OLIMEX/ESP32-EVB/HARDWARE/REV-K2/3d/User Library-GP1UE26.STEP

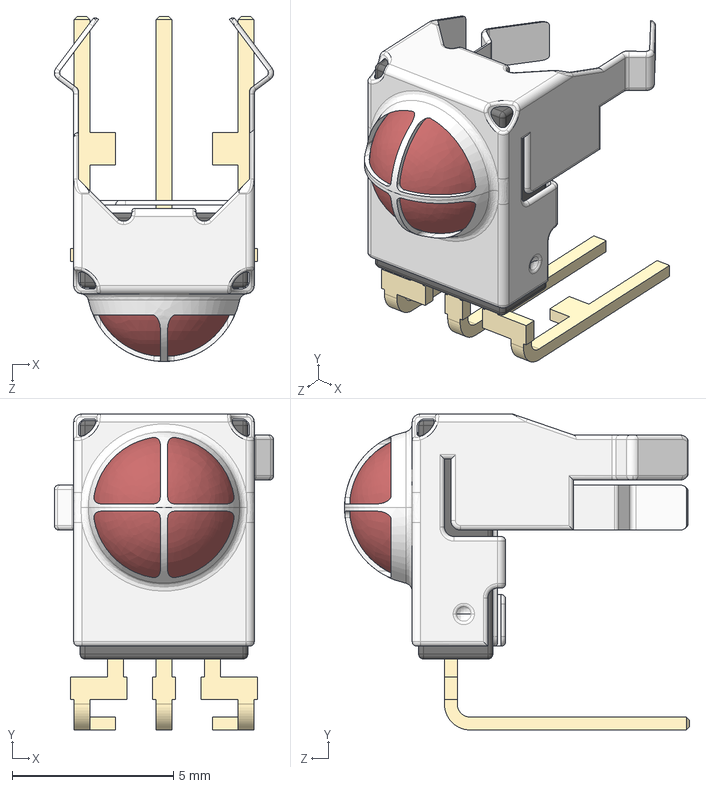
[picture p20: CAD file, 2020-01-02]
HARDWARE/REV-K2/3d/User Library-GP1UE26.STEP
6.80 x 9.80 x 10.7 mm
