OLIMEX/ESP32-EVB/HARDWARE/REV-K2/3d/BAT54.step

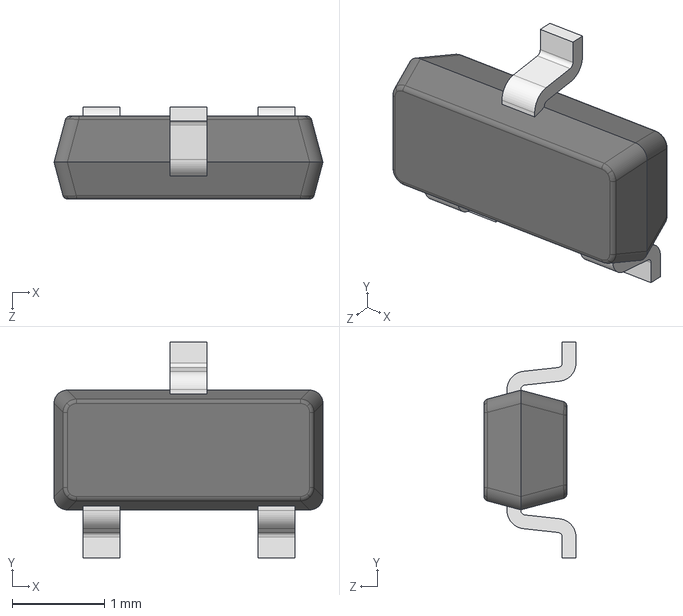
[picture p21: CAD file, 2020-01-02]
HARDWARE/REV-K2/3d/BAT54.step
2.92 x 2.34 x 1.00 mm
