OLIMEX/ESP32-EVB/HARDWARE/REV-K2/3d/TEConnectivity -ORWH-SH-124D1F000.stp

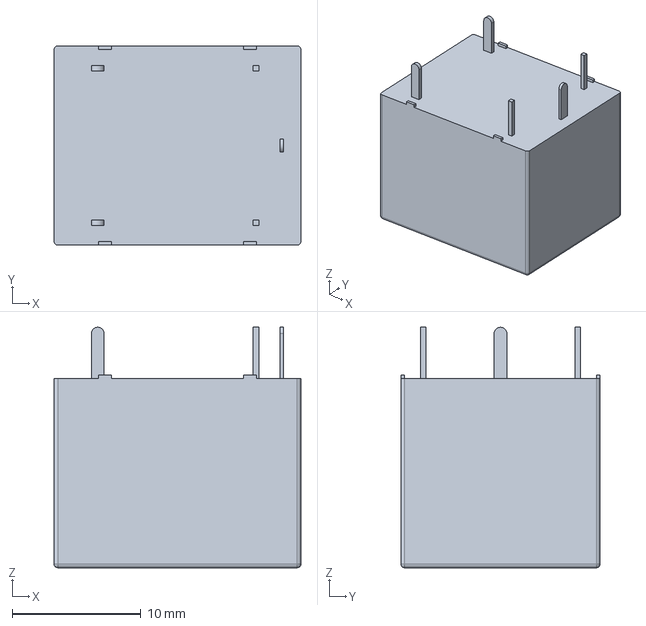
[picture p22: CAD file, 2020-01-02]
HARDWARE/REV-K2/3d/TEConnectivity -ORWH-SH-124D1F000.stp
19.2 x 15.5 x 18.7 mm
