OLIMEX/ESP32-EVB/HARDWARE/REV-K2/3d/SOT-23-5.step

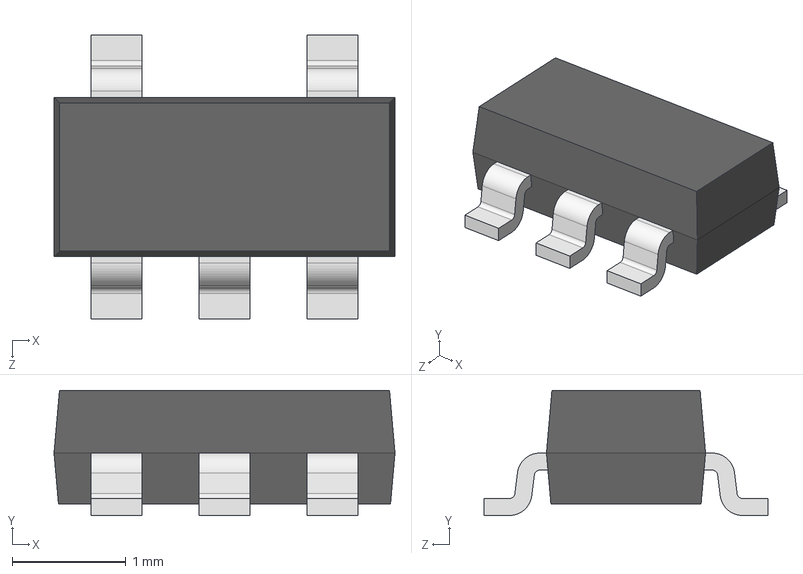
[picture p23: CAD file, 2020-01-02]
HARDWARE/REV-K2/3d/SOT-23-5.step
3.00 x 1.10 x 2.50 mm
