OLIMEX/ESP32-EVB/HARDWARE/REV-K2/3d/SO-8_150mil---SN65HVDA1050AQDRQ1.STEP

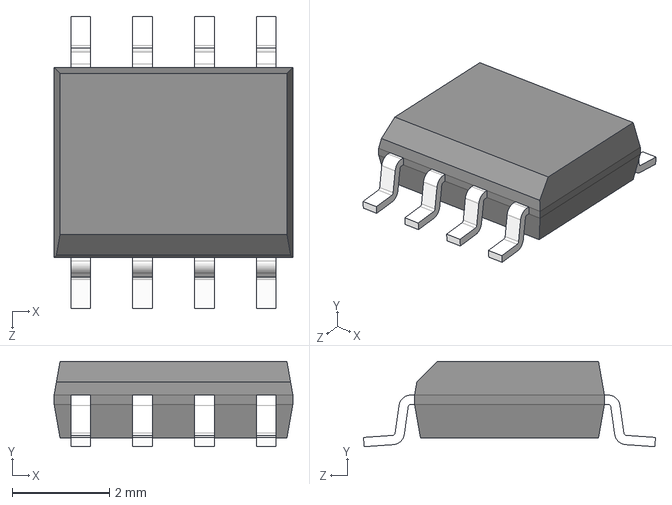
[picture p24: CAD file, 2020-01-02]
HARDWARE/REV-K2/3d/SO-8_150mil---SN65HVDA1050AQDRQ1.STEP
4.90 x 1.75 x 5.99 mm
