OLIMEX/ESP32-EVB/HARDWARE/REV-K2/3d/JST_B2B-PH-SM4-TB(DW02R).step

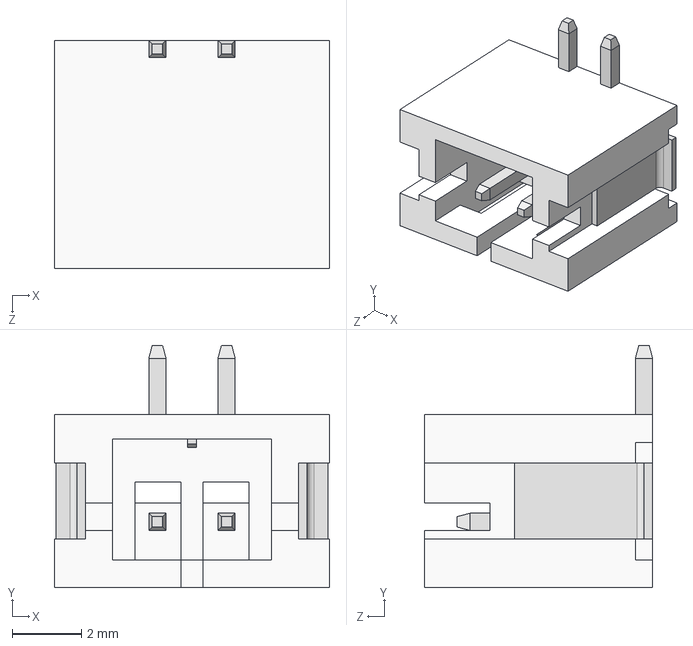
[picture p25: CAD file, 2020-01-02]
HARDWARE/REV-K2/3d/JST_B2B-PH-SM4-TB(DW02R).step
7.95 x 7.00 x 6.60 mm
