OLIMEX/ESP32-EVB/HARDWARE/REV-K2/3d/User_Library-Crystal_HC49_US-SM.step

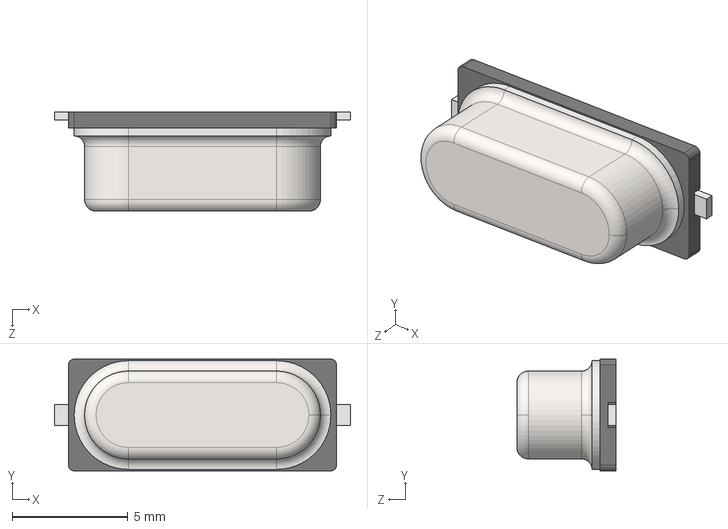
[picture p27: CAD file, 2020-01-02]
HARDWARE/REV-K2/3d/User_Library-Crystal_HC49_US-SM.step
12.8 x 4.83 x 4.30 mm
