OLIMEX/ESP32-EVB/HARDWARE/REV-K2/3d/BH-10__64.step

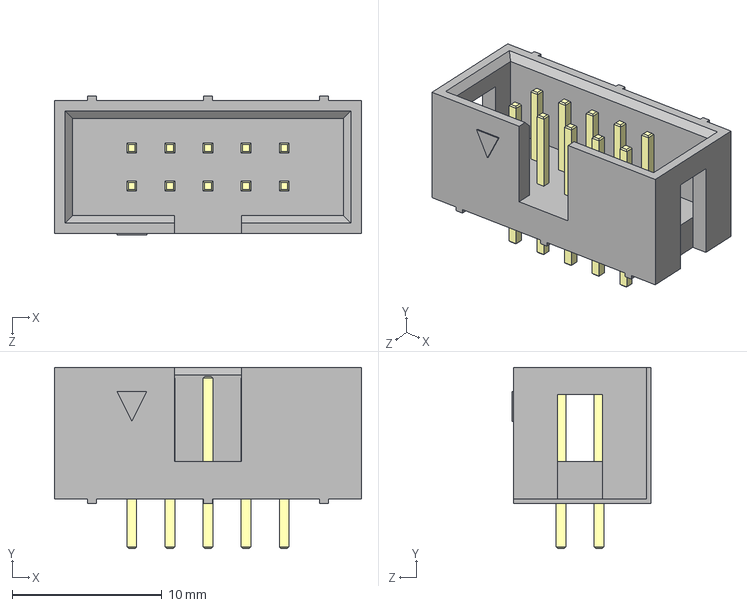
[picture p28: CAD file, 2020-01-02]
HARDWARE/REV-K2/3d/BH-10__64.step
20.5 x 12.1 x 9.30 mm
