OLIMEX/ESP32-EVB/HARDWARE/REV-K2/3d/SOD123.step

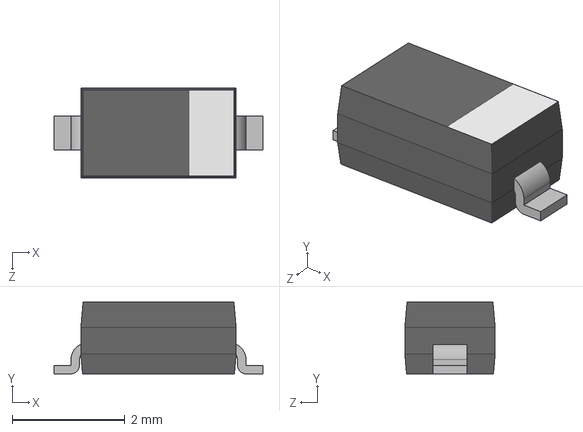
[picture p29: CAD file, 2020-01-02]
HARDWARE/REV-K2/3d/SOD123.step
3.70 x 1.27 x 1.60 mm
