OLIMEX/ESP32-EVB/HARDWARE/REV-K2/3d/pj-102ah.stp

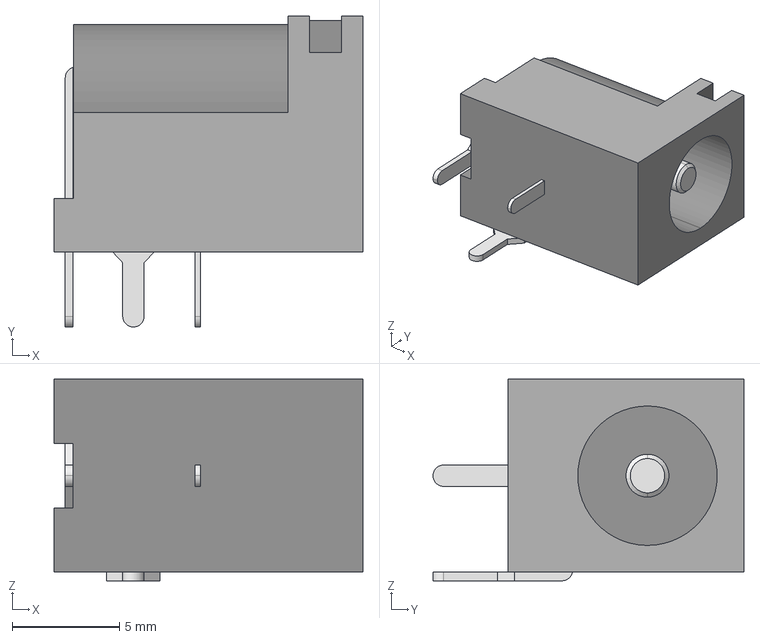
[picture p30: CAD file, 2020-01-02]
HARDWARE/REV-K2/3d/pj-102ah.stp
14.4 x 14.5 x 9.40 mm
