OLIMEX/ESP32-EVB/HARDWARE/REV-K2/3d/esp-wroom-32.step

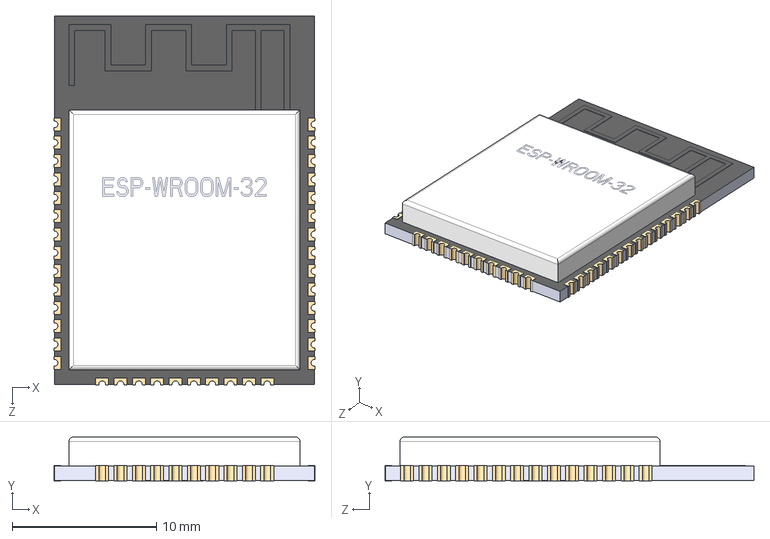
[picture p31: CAD file, 2020-01-02]
HARDWARE/REV-K2/3d/esp-wroom-32.step
18.1 x 3.04 x 25.5 mm
