OLIMEX/ESP32-EVB/HARDWARE/REV-H/ESP32-EVB_Rev_H-BOM.pdf

ESP32-EVB_Rev_H-BOM | 04/24/2019

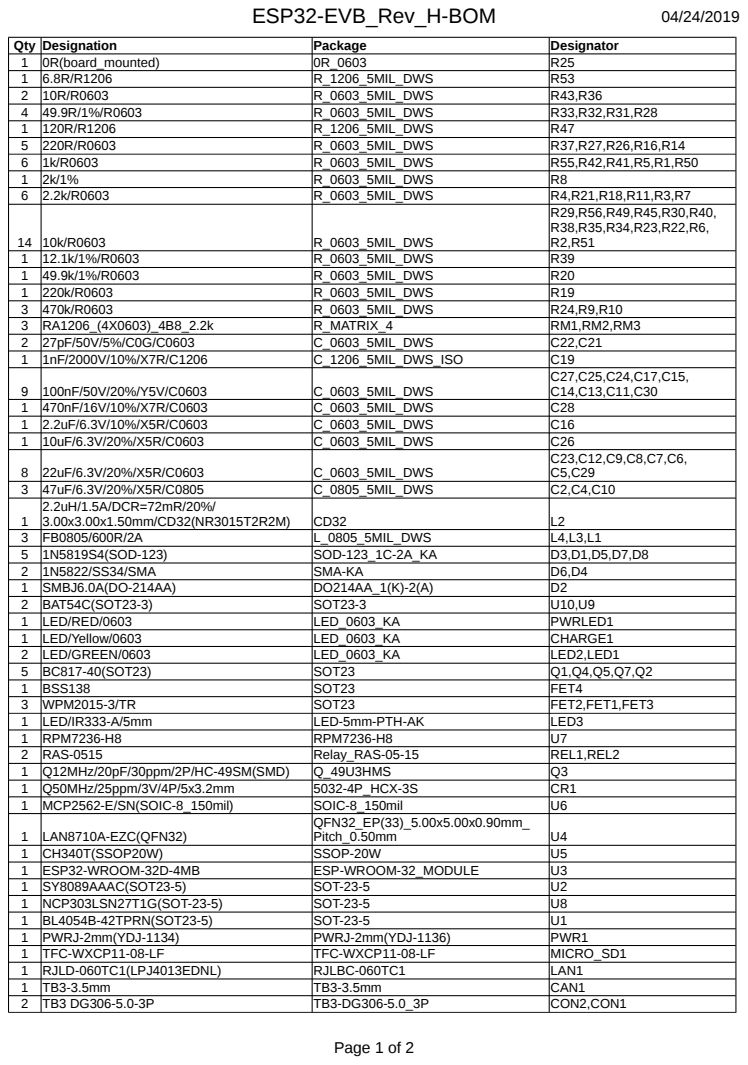
[picture p37: page 1]

| ESP32-EVB_Rev_H-BOM | 04/24/2019
1 BH10S | UEXT_ML10 | UEXT1
1 MISB-SWMM-5B-LF(USB_MICRO) | USB-MICRO_MISB-SWMM-5B_LF | USB-UART1
1 DW02R | LIPO_BAT-CON2DW02R | BAT1
2 T1107A(6x3,8x2,5MM) | T1107A(6x3,8x2,5MM) | RST1,BUT1
2 Opened | SJ | CAN_T1,PHY_RST1
1 Closed(1-2)/Opened(2-3) | SJ_2_SMALL_12_TIED | 5.0V/3.3V1
1 Opened(2-3)/Soldered(1-2) | SJ_2_SMALL | BAT/BUT1
1 NA(1k/R0603) | R_0603_5MIL_DWS | R57
5 NA/R0603 | R_0603_5MIL_DWS | R44,R54,R48,R46,R17
2 NA(47uF/6.3V/20%/X5R/C0805) | C_0805_5MIL_DWS | C3,C1
1 NA(1nF/2000V/10%/X7R/C1206) | C_1206_5MIL_DWS_ISO | C20
1 NA(HN2x20) | HN2x20 | EXT1
1 NA(TB2 DG306-5.0-2P) | TB2-DG306-5.0_2P | PWR2
1 NA(10uF/6.3V/20%/X5R/C0603) | C_0603_5MIL_DWS | C18
1 NA(FB0805/600R/2A) | L_0805_5MIL_DWS | L5
