OLIMEX/ESP32-EVB/HARDWARE/REV-H/ESP32-EVB_Rev_H.pdf

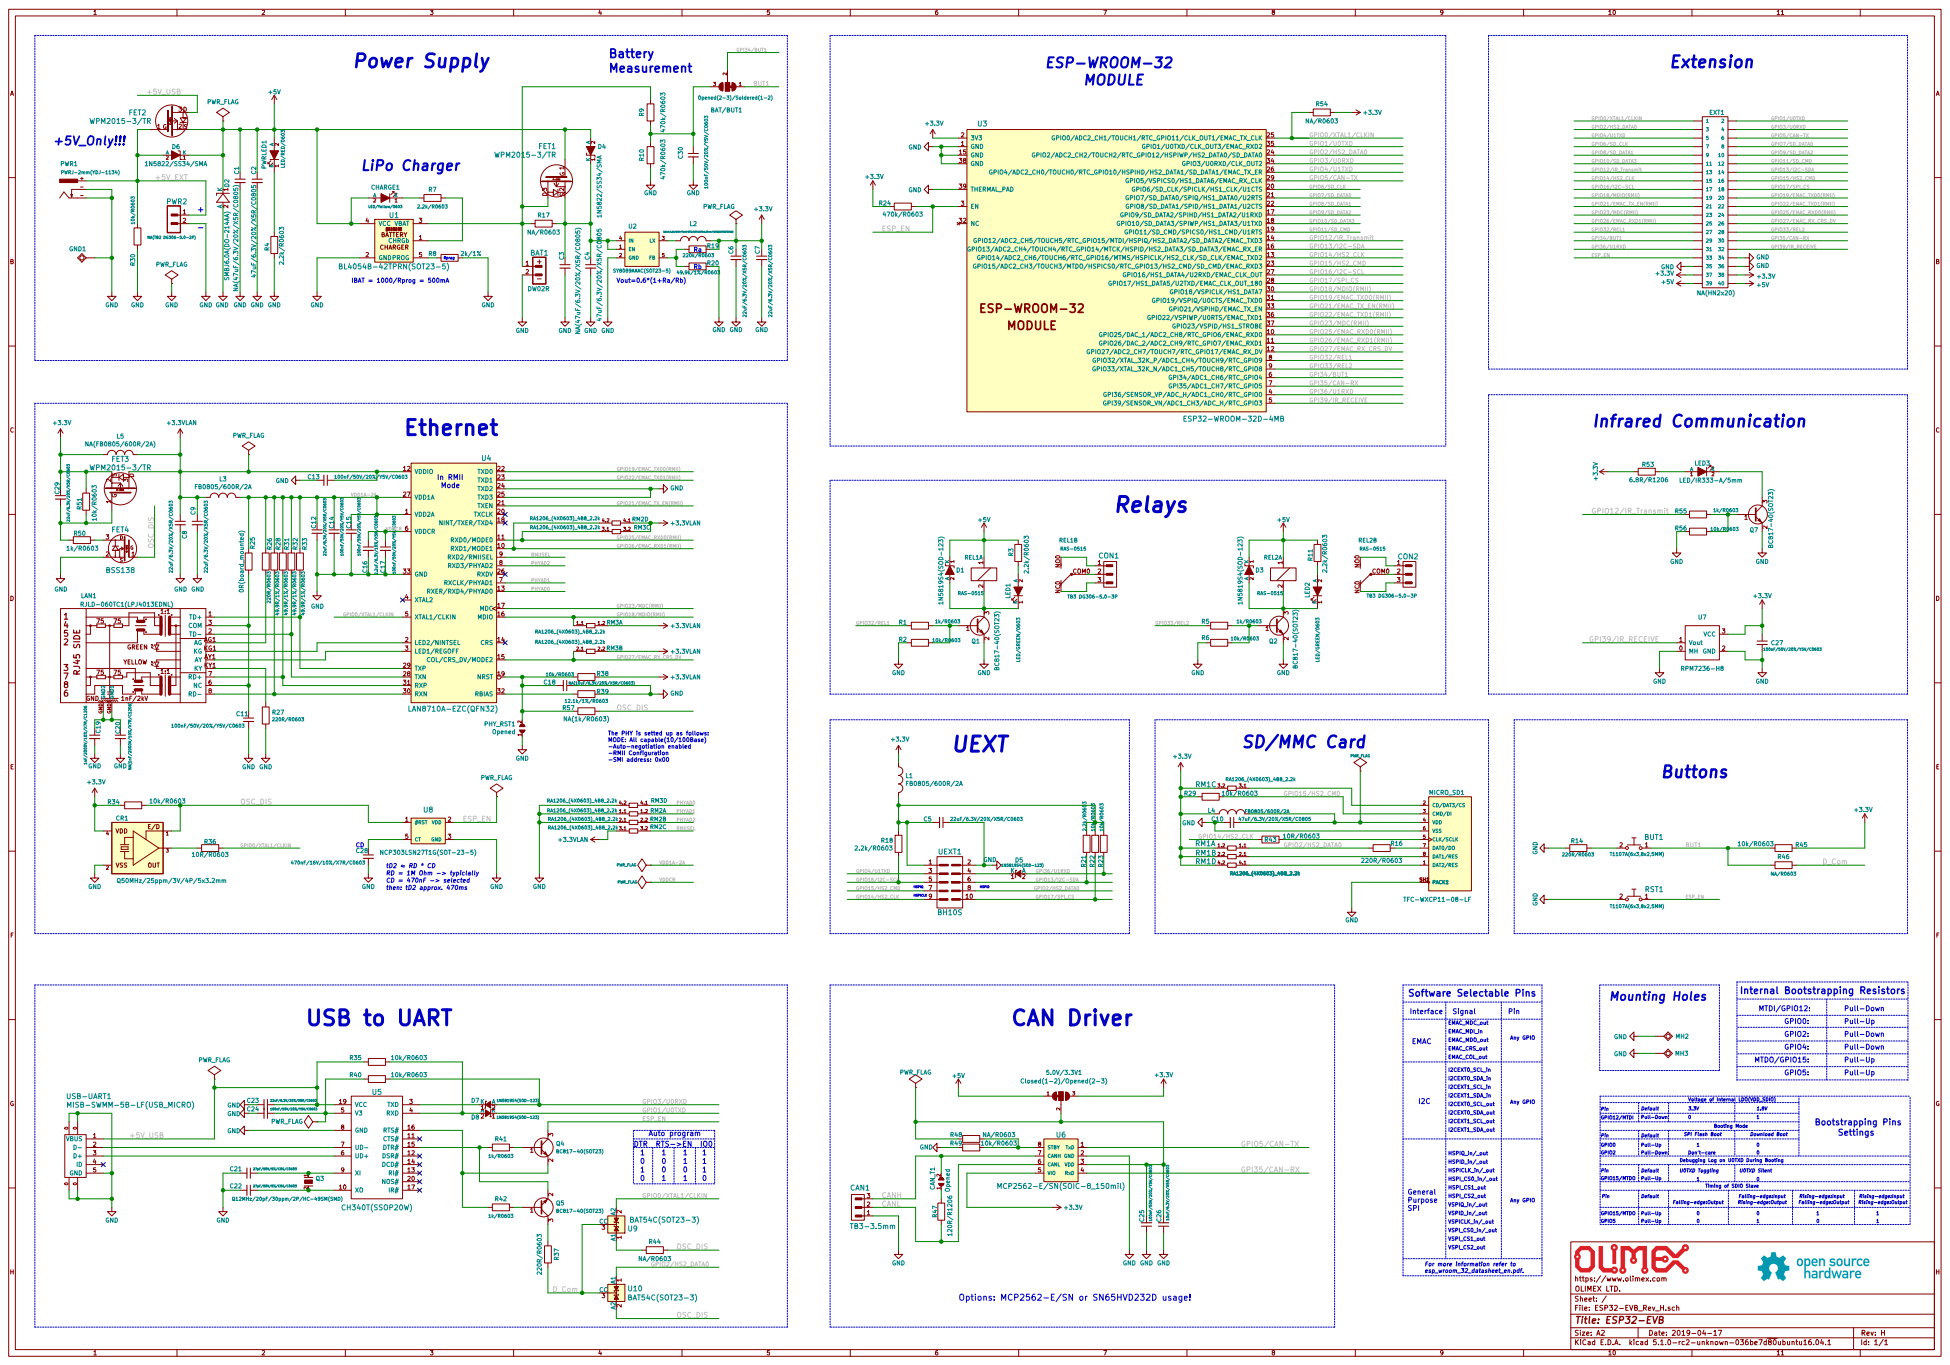
[picture p38: page 1]

2 PWRLED1 LED/RED/0603 GND GND GND GND GND

VDDCR The PHY is setted up as follows: MODE: All capable(10/100Base)

RD = 1M Ohm -> typiclally CD = 470nF -> selected

MISB-SWMM-5B-LF(USB_MICRO) GND

File: ESP32-EVB_Rev_H.sch Sheet: / OLIMEX LTD. https://www.olimex.com

Options: MCP2562-E/SN or SN65HVD232D usage!
