OLIMEX/ESP32-EVB/HARDWARE/REV-F/ESP32-EVB_Rev_F.pdf

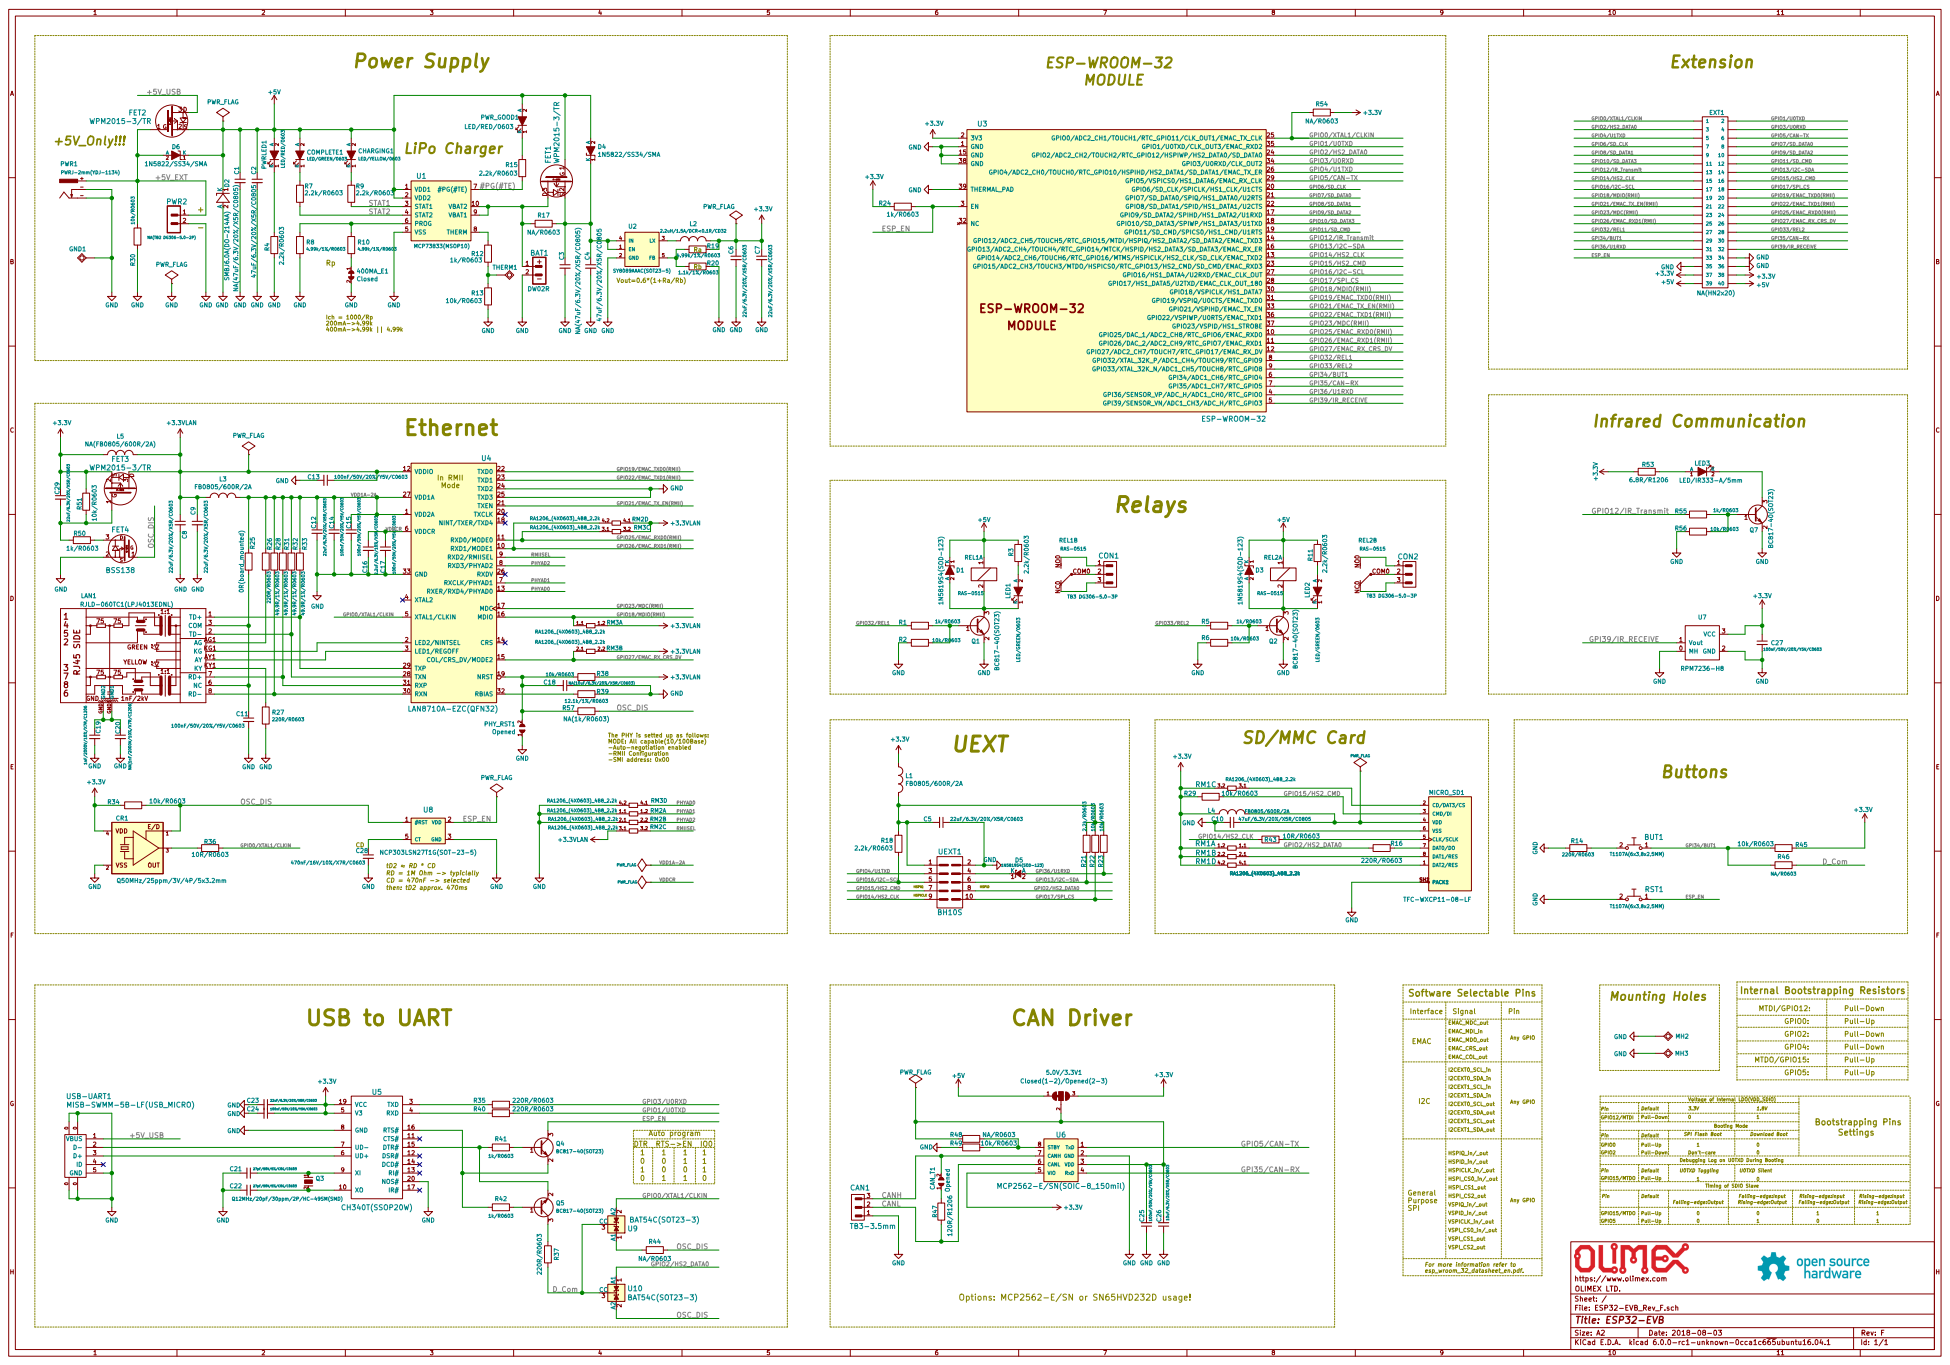
[picture p40: page 1]

2 PWRLED1 LED/RED/0603 GND GND GND GND GND

2.2uH/1.5A/DCR<0.1R/CD32 R19
GPIO13/I2C-SDA GPIO19/EMAC_TXD0(RMII) GPIO22/EMAC_TXD1(RMII) GPIO21/EMAC_TX_EN(RMII) GND

VDDCR The PHY is setted up as follows: MODE: All capable(10/100Base)
-Auto-negotiation enabled
-RMII Configuration
-SMI address: 0x00

PWR_FLAG
DAT2/RES 1 CD/DAT3/CS 2 CMD/DI 3 VDD 4 CLK/SCLK 5 VSS 6 DAT0/DO 7 DAT1/RES 8 PACK1 SH1 PACK2 SH2MICRO_SD1 TFC-WXCP11-08-LF

RD = 1M Ohm -> typiclally CD = 470nF -> selected

File: ESP32-EVB_Rev_F.sch Sheet: / OLIMEX LTD. https://www.olimex.com
