OLIMEX/ESP32-EVB/HARDWARE/REV-D/ESP32-EVB_Rev_D.pdf

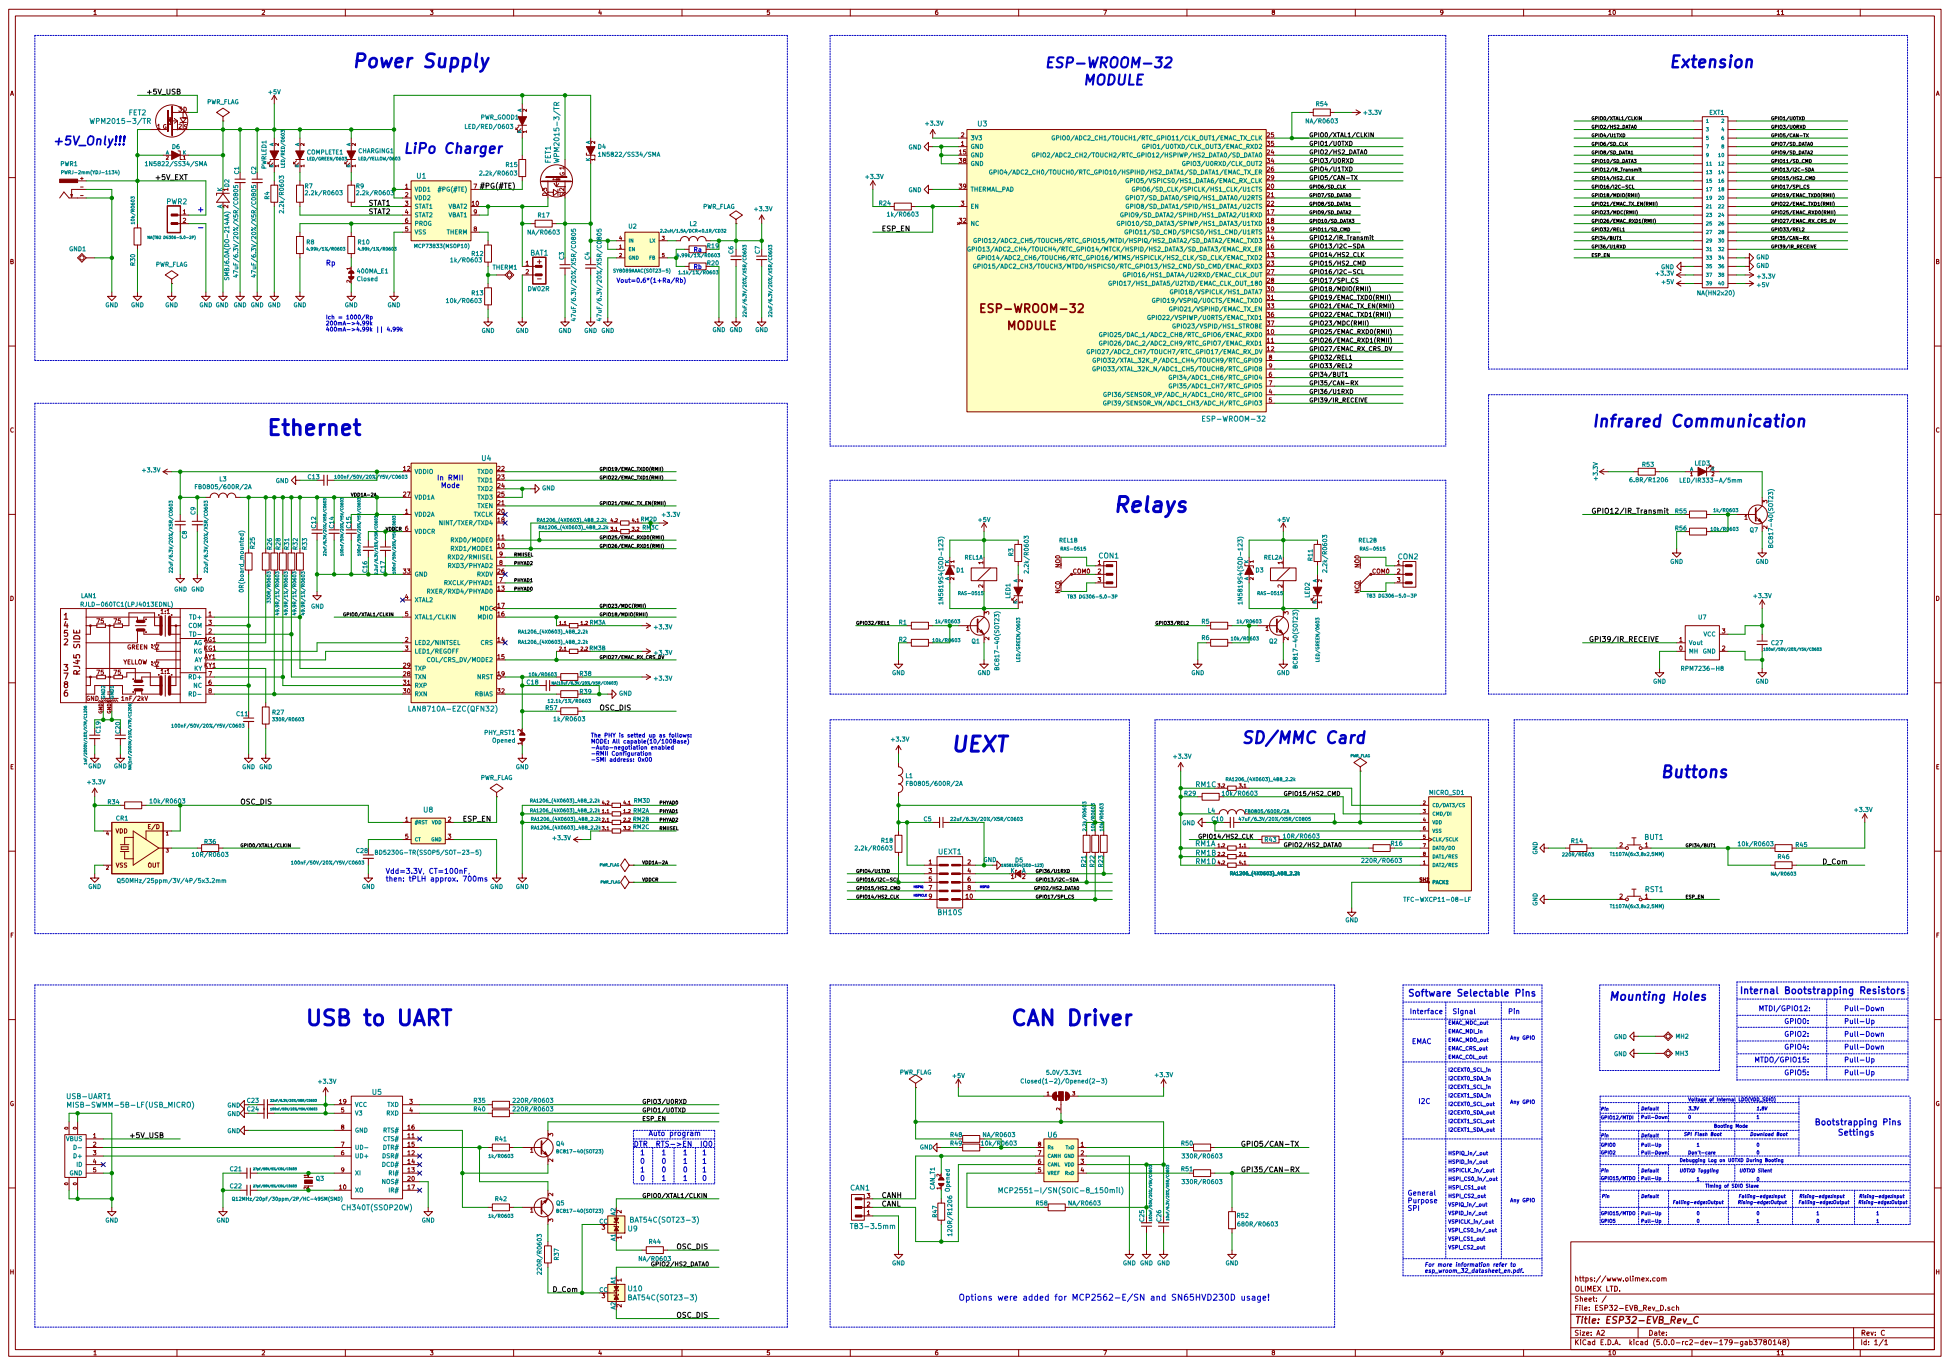
[picture p41: page 1]

2 PWRLED1 LED/RED/0603 GND GND GND GND GND

TD+ 1 TD- 2 COM 3 NC 6 RD+ 7 RD- 8 AG AG1 KG KG1 AY AY1 KY KY1 GND1 GND1 GND2 GND2 LAN1 RJLD-060TC1(LPJ4013EDNL)

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

MISB-SWMM-5B-LF(USB_MICRO) GND

VREF 5 CANL 6 CANH 7 Rs 8 U6 MCP2551-I/SN(SOIC-8_150mil) GND

File: ESP32-EVB_Rev_D.sch Sheet: / OLIMEX LTD. https://www.olimex.com
