OLIMEX/ESP32-EVB/SOFTWARE/ESP-IDF examples/toggle_relay/main/toggle_relay.c

// Copyright (c) 2017 Olimex LTD.
//
// GNU GENERAL PUBLIC LICENSE
//    Version 3, 29 June 2007
//
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
#include <stdio.h>
#include "freertos/FreeRTOS.h"
#include "driver/gpio.h"

#define OLIMEX_REL1_PIN     32
#define OLIMEX_REL2_PIN     33
#define OLIMEX_BUT_PIN      34

/* You can run menuconfig to change relay */
#if defined CONFIG_RELAY_1
#define RELAY_GPIO OLIMEX_REL1_PIN
#else
#define RELAY_GPIO OLIMEX_REL2_PIN
#endif

/**
 * @brief gpio_isr_handler  Handle button press interrupt
 */
static void IRAM_ATTR gpio_isr_handler(void* arg)
{
    gpio_set_level(RELAY_GPIO, !gpio_get_level(OLIMEX_BUT_PIN));
}

/**
 * @brief app_main          Application entry point
 */
void app_main()
{

    /* Make pads GPIO */
    gpio_reset_pin(RELAY_GPIO);
    gpio_reset_pin(OLIMEX_BUT_PIN);

    /* Set the Relay as a push/pull output */
    gpio_set_direction(RELAY_GPIO, GPIO_MODE_OUTPUT);

    /* Set Button as input */
    gpio_set_direction(OLIMEX_BUT_PIN, GPIO_MODE_INPUT);
    /* Enable interrupt on both edges */
    gpio_set_intr_type(OLIMEX_BUT_PIN, GPIO_INTR_ANYEDGE);

    /* Install ISR routine */
    gpio_install_isr_service(ESP_INTR_FLAG_LOWMED);
    gpio_isr_handler_add(OLIMEX_BUT_PIN, gpio_isr_handler, 0);



}
