OLIMEX/ESP32-EVB/SOFTWARE/ESP-IDF examples/ESP32-EVB_clock/components/hd44780/hd44780.c

/*
 * Copyright (c) 2016 Ruslan V. Uss <unclerus@gmail.com>
 *
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
 * THIS SOFTWARE IS PROVIDED BY THE COPYRIGHT HOLDERS AND CONTRIBUTORS "AS IS"
 * AND ANY EXPRESS OR IMPLIED WARRANTIES, INCLUDING, BUT NOT LIMITED TO, THE
 * IMPLIED WARRANTIES OF MERCHANTABILITY AND FITNESS FOR A PARTICULAR PURPOSE ARE
 * DISCLAIMED. IN NO EVENT SHALL THE COPYRIGHT HOLDER OR CONTRIBUTORS BE LIABLE
 * FOR ANY DIRECT, INDIRECT, INCIDENTAL, SPECIAL, EXEMPLARY, OR CONSEQUENTIAL
 * DAMAGES (INCLUDING, BUT NOT LIMITED TO, PROCUREMENT OF SUBSTITUTE GOODS OR
 * SERVICES; LOSS OF USE, DATA, OR PROFITS; OR BUSINESS INTERRUPTION) HOWEVER
 * CAUSED AND ON ANY THEORY OF LIABILITY, WHETHER IN CONTRACT, STRICT LIABILITY,
 * OR TORT (INCLUDING NEGLIGENCE OR OTHERWISE) ARISING IN ANY WAY OUT OF THE USE
 * OF THIS SOFTWARE, EVEN IF ADVISED OF THE POSSIBILITY OF SUCH DAMAGE.
 */

/**
 * @file hd44780.c
 *
 * ESP-IDF driver for HD44780 compatible LCD text displays
 *
 * Ported from esp-open-rtos
 *
 * Copyright (c) 2016 Ruslan V. Uss <unclerus@gmail.com>
 * 
 * Edited for New Haven Display NHD-0420DZA-AB5 by Brian Alano, Solar Stik, Inc.
 *
 * BSD Licensed as described in the file LICENSE
 */
#include <string.h>
#include <esp_system.h>
#include <esp_idf_lib_helpers.h>
#if CONFIG_IDF_TARGET_ESP32
#include <esp32/rom/ets_sys.h>
#elif CONFIG_IDF_TARGET_ESP32S2
#include <esp32s2/rom/ets_sys.h>
#elif CONFIG_IDF_TARGET_ESP32S3
#include <esp32s3/rom/ets_sys.h>
#elif CONFIG_IDF_TARGET_ESP32C3
#include <esp32c3/rom/ets_sys.h>
#elif CONFIG_IDF_TARGET_ESP32H2
#include <esp32h2/rom/ets_sys.h>
#elif CONFIG_IDF_TARGET_ESP32C2
#include <esp32c2/rom/ets_sys.h>
#endif
#include "hd44780.h"

#define MS 1000

#define BV(x) (1 << (x))
#define GPIO_BIT(x) (1ULL << (x))

#define DELAY_CMD_LONG  (3 * MS) // <=2ms according to datasheet?
#define DELAY_CMD_SHORT (800)     // <=600us according to datasheet?
#define DELAY_TOGGLE    (20) // (1)  // Address setup time and data hold time are 20 ns. Most is longer    // E cycle time >= 1μs, E pulse width >= 450ns, Data set-up time >= 195ns
#define DELAY_INIT      (5 * MS)

#define CMD_CLEAR        0x01 // 2 ms
#define CMD_RETURN_HOME  0x02 // 600 us
#define CMD_ENTRY_MODE   0x04 // 600 us
#define CMD_DISPLAY_CTRL 0x08 // 600 us
#define CMD_SHIFT        0x10 // 600 us
#define CMD_FUNC_SET     0x20 // 0x00001x10xxb 600 us
#define CMD_CGRAM_ADDR   0x40 // 600 us
#define CMD_DDRAM_ADDR   0x80 // 600 us

#define ARG_MOVE_RIGHT 0x04
#define ARG_MOVE_LEFT 0x00
#define CMD_SHIFT_LEFT  (CMD_SHIFT | CMD_DISPLAY_CTRL | ARG_MOVE_LEFT)
#define CMD_SHIFT_RIGHT (CMD_SHIFT | CMD_DISPLAY_CTRL | ARG_MOVE_RIGHT)

// CMD_ENTRY_MODE
#define ARG_EM_INCREMENT    BV(1)
#define ARG_EM_SHIFT        (1)

// CMD_DISPLAY_CTRL
#define ARG_DC_DISPLAY_ON   BV(2)
#define ARG_DC_CURSOR_ON    BV(1)
#define ARG_DC_CURSOR_BLINK (1)

// CMD_FUNC_SET
#define ARG_FS_8_BIT        BV(4)
#define ARG_FS_2_LINES      BV(3)
#define ARG_FS_FONT_5X10    BV(2)

#define init_delay()   do { ets_delay_us(DELAY_INIT); } while (0)
#define short_delay()  do { ets_delay_us(DELAY_CMD_SHORT); } while (0)
#define long_delay()   do { ets_delay_us(DELAY_CMD_LONG); } while (0)
#define toggle_delay() do { ets_delay_us(DELAY_TOGGLE); } while (0)

#define CHECK_ARG(VAL) do { if (!(VAL)) return ESP_ERR_INVALID_ARG; } while (0)
#define CHECK(x) do { esp_err_t __; if ((__ = x) != ESP_OK) return __; } while (0)

static const uint8_t line_addr[] = { 0x00, 0x40, 0x14, 0x54 };

static esp_err_t write_nibble(const hd44780_t *lcd, uint8_t b, bool rs)
{
    if (lcd->write_cb)
    {
        uint8_t data = (((b >> 3) & 1) << lcd->pins.d7)
                     | (((b >> 2) & 1) << lcd->pins.d6)
                     | (((b >> 1) & 1) << lcd->pins.d5)
                     | ((b & 1) << lcd->pins.d4)
                     | (rs ? 1 << lcd->pins.rs : 0)
                     | (lcd->backlight ? 1 << lcd->pins.bl : 0);
        CHECK(lcd->write_cb(lcd, data | (1 << lcd->pins.e)));
        toggle_delay();
        CHECK(lcd->write_cb(lcd, data));
    }
    else
    {
        CHECK(gpio_set_level(lcd->pins.rs, rs));
        ets_delay_us(1); // Address Setup time >= 60ns.
        CHECK(gpio_set_level(lcd->pins.e, true));
        CHECK(gpio_set_level(lcd->pins.d7, (b >> 3) & 1));
        CHECK(gpio_set_level(lcd->pins.d6, (b >> 2) & 1));
        CHECK(gpio_set_level(lcd->pins.d5, (b >> 1) & 1));
        CHECK(gpio_set_level(lcd->pins.d4, b & 1));
        toggle_delay();
        CHECK(gpio_set_level(lcd->pins.e, false));
    }

    return ESP_OK;
}

static esp_err_t write_byte(const hd44780_t *lcd, uint8_t b, bool rs)
{
    CHECK(write_nibble(lcd, b >> 4, rs));
    CHECK(write_nibble(lcd, b, rs));

    return ESP_OK;
}

esp_err_t hd44780_init(const hd44780_t *lcd)
{
    CHECK_ARG(lcd && lcd->lines > 0 && lcd->lines < 5);

    if (!lcd->write_cb)
    {
        gpio_config_t io_conf;
        memset(&io_conf, 0, sizeof(gpio_config_t));
        io_conf.mode = GPIO_MODE_OUTPUT;
        io_conf.pin_bit_mask =
                GPIO_BIT(lcd->pins.rs) |
                GPIO_BIT(lcd->pins.e) |
                GPIO_BIT(lcd->pins.d4) |
                GPIO_BIT(lcd->pins.d5) |
                GPIO_BIT(lcd->pins.d6) |
                GPIO_BIT(lcd->pins.d7);
                
        if (lcd->pins.bl != HD44780_NOT_USED)
            io_conf.pin_bit_mask |= GPIO_BIT(lcd->pins.bl);
        CHECK(gpio_config(&io_conf));
    }

    // switch to 4 bit mode
    for (uint8_t i = 0; i < 3; i ++)
    {
        CHECK(write_nibble(lcd, (CMD_FUNC_SET | ARG_FS_8_BIT) >> 4, false));
        init_delay();
    }
    CHECK(write_nibble(lcd, CMD_FUNC_SET >> 4, false));
    short_delay();

    // Specify the number of display lines and character font
    CHECK(write_byte(lcd,
        CMD_FUNC_SET
            | (lcd->lines > 1 ? ARG_FS_2_LINES : 0)
            | (lcd->font == HD44780_FONT_5X10 ? ARG_FS_FONT_5X10 : 0),
        false));
    short_delay();
    // Display off
    CHECK(hd44780_control(lcd, false, false, false));
    // Clear
    CHECK(hd44780_clear(lcd));
    // Entry mode set
    CHECK(write_byte(lcd, CMD_ENTRY_MODE | ARG_EM_INCREMENT, false));
    short_delay();
    // Display on
    CHECK(hd44780_control(lcd, true, false, false));

    return ESP_OK;
}

esp_err_t hd44780_control(const hd44780_t *lcd, bool on, bool cursor, bool cursor_blink)
{
    CHECK_ARG(lcd);

    CHECK(write_byte(lcd,
        CMD_DISPLAY_CTRL
            | (on ? ARG_DC_DISPLAY_ON : 0)
            | (cursor ? ARG_DC_CURSOR_ON : 0)
            | (cursor_blink ? ARG_DC_CURSOR_BLINK : 0),
        false));
    short_delay();

    return ESP_OK;
}

esp_err_t hd44780_clear(const hd44780_t *lcd)
{
    CHECK_ARG(lcd);

    CHECK(write_byte(lcd, CMD_CLEAR, false));
    long_delay();

    return ESP_OK;
}

esp_err_t hd44780_gotoxy(const hd44780_t *lcd, uint8_t col, uint8_t line)
{
    CHECK_ARG(lcd && line < lcd->lines && line < sizeof(line_addr));

    CHECK(write_byte(lcd, CMD_DDRAM_ADDR + line_addr[line] + col, false));
    short_delay();

    return ESP_OK;
}

esp_err_t hd44780_putc(const hd44780_t *lcd, char c)
{
    CHECK_ARG(lcd);

    CHECK(write_byte(lcd, c, true));
    short_delay();

    return ESP_OK;
}

esp_err_t hd44780_puts(const hd44780_t *lcd, const char *s)
{
    CHECK_ARG(lcd && s);

    while (*s)
    {
        CHECK(hd44780_putc(lcd, *s));
        s++;
    }

    return ESP_OK;
}

esp_err_t hd44780_switch_backlight(hd44780_t *lcd, bool on)
{
    CHECK_ARG(lcd);
    if (lcd->pins.bl == HD44780_NOT_USED)
        return ESP_ERR_NOT_SUPPORTED;

    if (!lcd->write_cb)
        CHECK(gpio_set_level(lcd->pins.bl, on));
    else
        CHECK(lcd->write_cb(lcd, on ? BV(lcd->pins.bl) : 0));

    lcd->backlight = on;

    return ESP_OK;
}

esp_err_t hd44780_upload_character(const hd44780_t *lcd, uint8_t num, const uint8_t *data)
{
    CHECK_ARG(lcd && data && num < 8);

    uint8_t bytes = lcd->font == HD44780_FONT_5X8 ? 8 : 10;
    CHECK(write_byte(lcd, CMD_CGRAM_ADDR + num * bytes, false));
    short_delay();
    for (uint8_t i = 0; i < bytes; i ++)
    {
        CHECK(write_byte(lcd, data[i], true));
        short_delay();
    }

    CHECK(hd44780_gotoxy(lcd, 0, 0));

    return ESP_OK;
}

esp_err_t hd44780_scroll_left(const hd44780_t *lcd)
{
    CHECK_ARG(lcd);

    CHECK(write_byte(lcd, CMD_SHIFT_LEFT, false));
    short_delay();

    return ESP_OK;
}

esp_err_t hd44780_scroll_right(const hd44780_t *lcd)
{
    CHECK_ARG(lcd);

    CHECK(write_byte(lcd, CMD_SHIFT_RIGHT, false));
    short_delay();

    return ESP_OK;
}
